ASM-FAU/Multimodal-Bracelet/CAD/v1/Sub/sub_cover_emg_only.stl

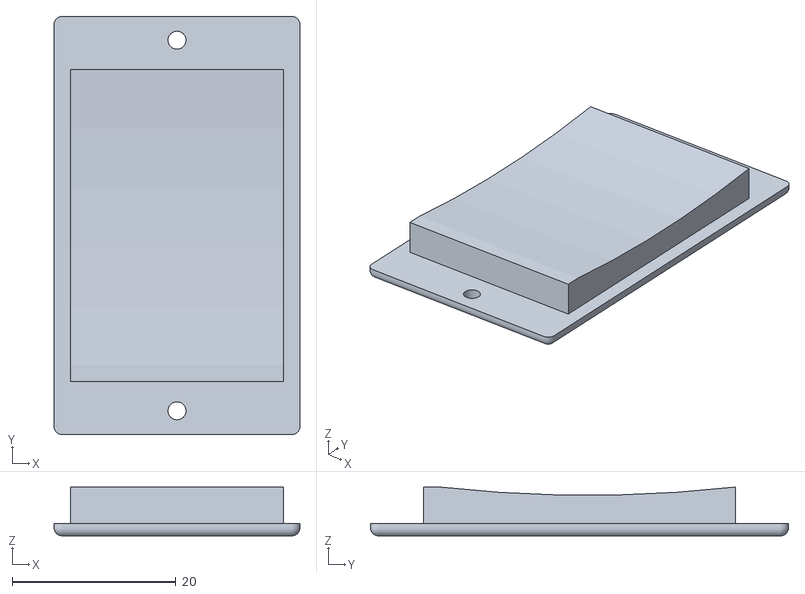
[picture p15: CAD file, 2024-08-16, an earlier design]
CAD/v1/Sub/sub_cover_emg_only.stl
30.0 x 51.0 x 5.96
